BrunoFenzl/CubieKid/photos/CubieKid_2.jpg

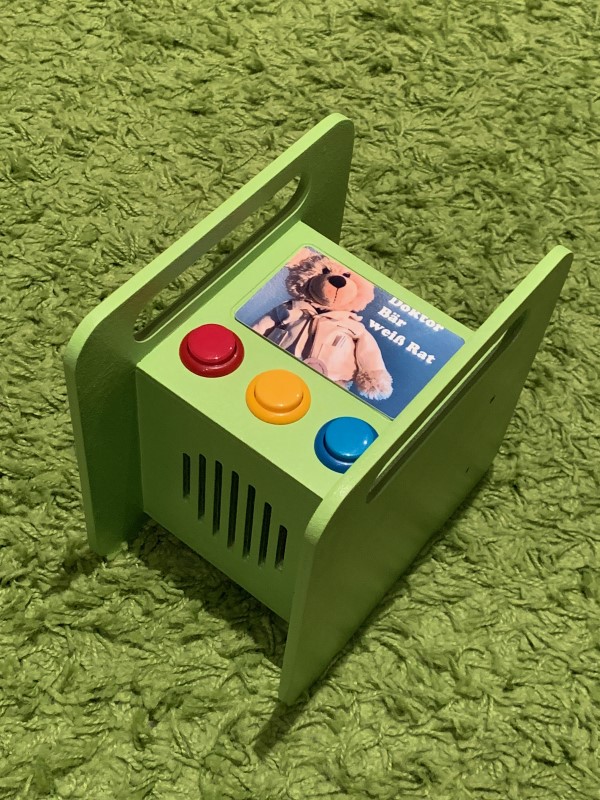
photos/CubieKid_2.jpg
