BrunoFenzl/CubieKid/photos/PCB_1.jpg

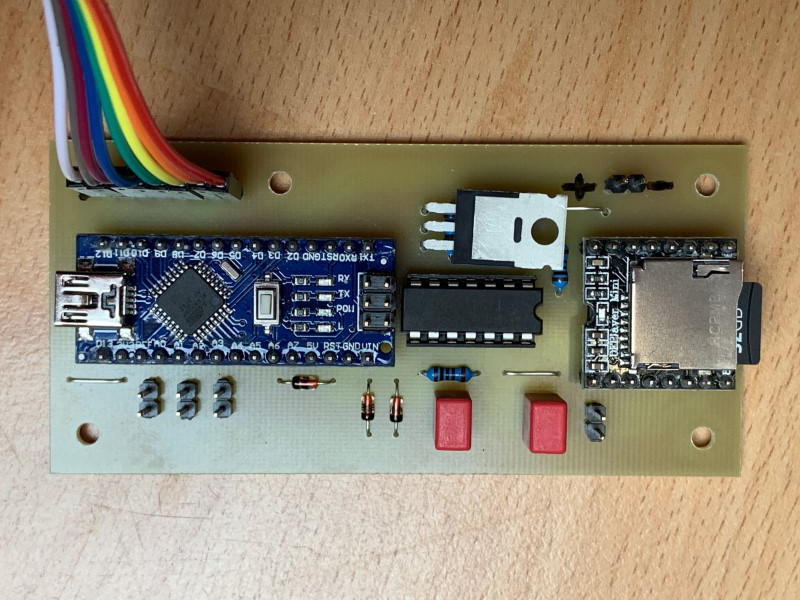
photos/PCB_1.jpg
