BrunoFenzl/CubieKid/photos/RFID-Reader.jpg

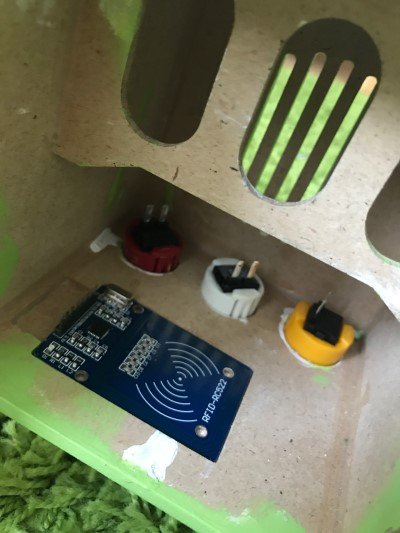
photos/RFID-Reader.jpg
